Irony95/cableTester/Software/home_page.py

from button import button
from config import TEST_PROFILES
from ili9341 import Display, color565
from tools import draw_header


TITLE = "WINDSHEAR CABLE TESTER"
BUTTONS = [
    button(
        164 * col + 0,
        76 * row + 48,
        156,
        68,
        text=TEST_PROFILES[row * 2 + col]["label"],
        task="diagram_page",
        task_args=(TEST_PROFILES[row * 2 + col],),
        colour=color565(255, 255, 0),
    )
    for row in range(2)
    for col in range(2)
]
BUTTONS.extend(
    [
        button(
            222,
            200,
            98,
            40,
            text=">>>",
            task="home_page2",
            colour=color565(255, 255, 255),
        ),
    ]
)


def main(display: Display):
    draw_header(
        display, TITLE, color565(0, 255, 0), color565(0, 0, 0), color565(0, 255, 0)
    )
    [btn.draw(display) for btn in BUTTONS]
