Irony95/cableTester/Software/pages.py

import home_page
import home_page2
import result_page
import details_page
import diagram_page


pages = {
    "home_page": home_page,
    "result_page": result_page,
    "details_page": details_page,
    "home_page2": home_page2,
    "diagram_page": diagram_page
}
